apfaudio/tiliqua/gateware/docs/_static/tiliqua-back.jpg

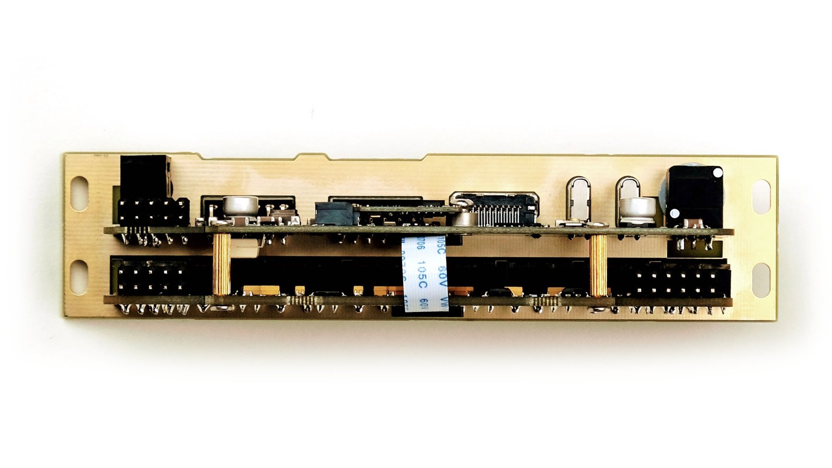
gateware/docs/_static/tiliqua-back.jpg
