apfaudio/tiliqua/gateware/docs/_static/devlog_mar25/plots/mipi_ttl/mipi_100khz.png

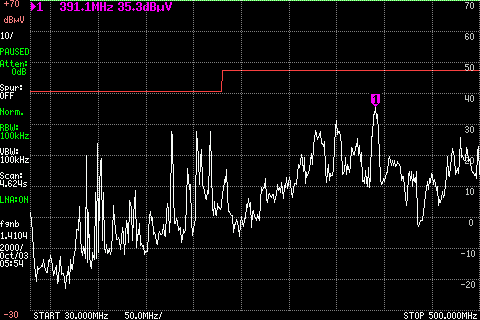
gateware/docs/_static/devlog_mar25/plots/mipi_ttl/mipi_100khz.png
