apfaudio/tiliqua/gateware/docs/_static/devlog_mar25/plots/mipi_ttl/ttl_100khz.png

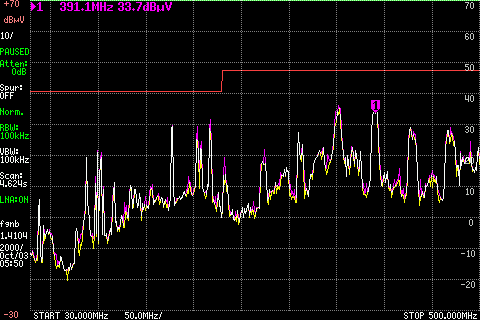
gateware/docs/_static/devlog_mar25/plots/mipi_ttl/ttl_100khz.png
