apfaudio/tiliqua/gateware/docs/_static/devlog_mar25/plots/r4_ea8c_850khz.png

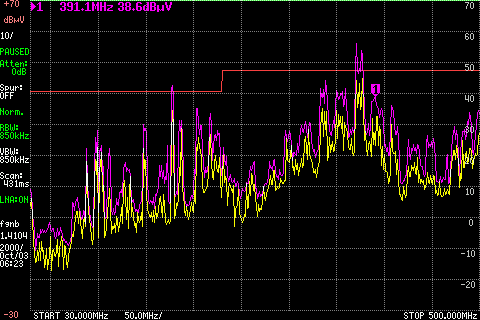
gateware/docs/_static/devlog_mar25/plots/r4_ea8c_850khz.png
