apfaudio/tiliqua/gateware/docs/_static/devlog_mar25/plots/r4_main_macro_osc_0p1ssc_100khz.png

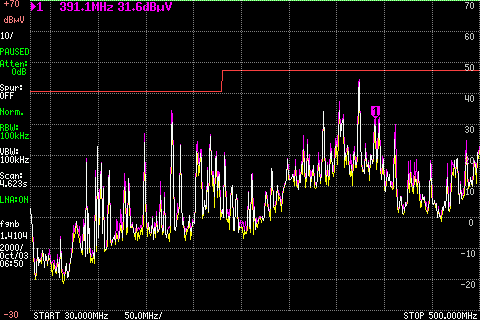
gateware/docs/_static/devlog_mar25/plots/r4_main_macro_osc_0p1ssc_100khz.png
