apfaudio/tiliqua/gateware/src/tiliqua/dsp.py

# Copyright (c) 2024 S. Holzapfel <me@sebholzapfel.com>
#
# SPDX-License-Identifier: CERN-OHL-S-2.0
#

"""Streaming DSP library with a strong focus on audio."""

import math

from amaranth              import *
from amaranth.lib          import wiring, data, stream, enum
from amaranth.lib.wiring   import In, Out
from amaranth.lib.fifo     import SyncFIFOBuffered, AsyncFIFOBuffered
from amaranth.lib.memory   import Memory
from amaranth.utils        import exact_log2, ceil_log2

from scipy import signal

from amaranth_future       import fixed
from tiliqua               import mac

from tiliqua.eurorack_pmod import ASQ # hardware native fixed-point sample type

# dummy values used to hook up to unused stream in/out ports, so they don't block forever
ASQ_READY = stream.Signature(ASQ, always_ready=True).flip().create()
ASQ_VALID = stream.Signature(ASQ, always_valid=True).create()

class Split(wiring.Component):

    """
    Consumes payloads from a single stream and splits it into multiple independent streams.
    This component may be instantiated in 2 modes depending on the value of :py:`replicate`:

    - **Channel splitter** (:py:`replicate == False`):
        The incoming stream has an :py:`data.ArrayLayout` signature. Each payload in the
        :py:`data.ArrayLayout` becomes an independent outgoing stream. :py:`n_channels`
        must match the number of payloads in the :py:`data.ArrayLayout`.

    - **Channel replicater** (:py:`replicate == True`):
        The incoming stream has a single payload. Each payload in the incoming stream
        is replicated and at the output appears as :py:`n_channels` independent streams,
        which produce the same values, however may be synchronized/consumed independently.

    This class is inspired by previous work in the lambdalib and LiteX projects.
    """

    def __init__(self, n_channels, replicate=False, source=None):
        """
        n_channels : int
            The number of independent output streams. See usage above.
        replicate : bool, optional
            See usage above.
        source : stream, optional
            Optional incoming stream to pass through to :py:`wiring.connect` on
            elaboration. This argument means you do not have to hook up :py:`self.i`
            and can make some pipelines a little easier to read.
        """
        self.n_channels = n_channels
        self.replicate  = replicate
        self.source     = source

        if self.replicate:
            super().__init__({
                "i": In(stream.Signature(ASQ)),
                "o": Out(stream.Signature(ASQ)).array(n_channels),
            })
        else:
            super().__init__({
                "i": In(stream.Signature(data.ArrayLayout(ASQ, n_channels))),
                "o": Out(stream.Signature(ASQ)).array(n_channels),
            })

    def elaborate(self, platform):
        m = Module()

        done = Signal(self.n_channels)

        m.d.comb += self.i.ready.eq(Cat([self.o[n].ready | done[n] for n in range(self.n_channels)]).all())
        m.d.comb += [self.o[n].valid.eq(self.i.valid & ~done[n]) for n in range(self.n_channels)]

        if self.replicate:
            m.d.comb += [self.o[n].payload.eq(self.i.payload) for n in range(self.n_channels)]
        else:
            m.d.comb += [self.o[n].payload.eq(self.i.payload[n]) for n in range(self.n_channels)]

        flow = [self.o[n].valid & self.o[n].ready
                for n in range(self.n_channels)]
        end  = Cat([flow[n] | done[n]
                    for n in range(self.n_channels)]).all()
        with m.If(end):
            m.d.sync += done.eq(0)
        with m.Else():
            for n in range(self.n_channels):
                with m.If(flow[n]):
                    m.d.sync += done[n].eq(1)

        if self.source is not None:
            wiring.connect(m, self.source, self.i)

        return m

    def wire_ready(self, m, channels):
        """Set out channels as permanently READY so they don't block progress."""
        for n in channels:
            wiring.connect(m, self.o[n], ASQ_READY)

class Merge(wiring.Component):

    """
    Consumes payloads from multiple independent streams and merges them into a single stream.

    This class is inspired by previous work in the lambdalib and LiteX projects.
    """

    def __init__(self, n_channels, sink=None):
        """
        n_channels : int
            The number of independent incoming streams.
        sink : stream, optional
            Optional outgoing stream to pass through to :py:`wiring.connect` on
            elaboration. This argument means you do not have to hook up :py:`self.o`
            and can make some pipelines a little easier to read.
        """
        self.n_channels = n_channels
        self.sink       = sink
        super().__init__({
            "i": In(stream.Signature(ASQ)).array(n_channels),
            "o": Out(stream.Signature(data.ArrayLayout(ASQ, n_channels))),
        })

    def elaborate(self, platform):
        m = Module()

        m.d.comb += [self.i[n].ready.eq(self.o.ready & self.o.valid) for n in range(self.n_channels)]
        m.d.comb += [self.o.payload[n].eq(self.i[n].payload) for n in range(self.n_channels)]
        m.d.comb += self.o.valid.eq(Cat([self.i[n].valid for n in range(self.n_channels)]).all())

        if self.sink is not None:
            wiring.connect(m, self.o, self.sink)

        return m

    def wire_valid(self, m, channels):
        """Set in channels as permanently VALID so they don't block progress."""
        for n in channels:
            wiring.connect(m, stream.Signature(ASQ, always_valid=True).create(), self.i[n])

def connect_remap(m, stream_o, stream_i, mapping):
    """
    Connect 2 streams, bypassing normal wiring.connect() checks
    that the signatures match. This allows easily remapping fields when
    you are trying to connect streams with different signatures.

    For example, say I have a stream with an ArrayLayout payload and want to
    map it to a different stream with a StructLayout payload, and the underlying
    bit-representation of both layouts do not match, I can remap using:

    .. code-block:: python

        dsp.connect_remap(m, vca_merge2a.o, vca0.i, lambda o, i : [
            i.payload.x   .eq(o.payload[0]),
            i.payload.gain.eq(o.payload[1] << 2)
        ])

    This is a bit of a hack. TODO perhaps implement this as a StreamConverter
    such that we can still use wiring.connect?.
    """

    m.d.comb += mapping(stream_o, stream_i) + [
        stream_i.valid.eq(stream_o.valid),
        stream_o.ready.eq(stream_i.ready)
    ]

def channel_remap(m, stream_o, stream_i, mapping_o_to_i):
    """
    Connect 2 streams of type :py:`data.ArrayLayout`, with different channel
    counts or channel indices. For example, to connect a source with 4 channels
    to a sink with 2 channels, mapping 0 to 0, 1 to 1, leaving 2 and 3 unconnected:

    .. code-block:: python

        s1 = stream.Signature(data.ArrayLayout(ASQ, 4)).create()
        s2 = stream.Signature(data.ArrayLayout(ASQ, 2)).create()
        dsp.channel_remap(m, s1, s2, {0: 0, 1: 1})

    This also works the other way around, to connect e.g. a source with 2 channels to
    a sink with 4 channels. The stream will make progress however the value of the
    payloads in any unmapped output channels is undefined.
    """
    def remap(o, i):
        connections = []
        for k in mapping_o_to_i:
            connections.append(i.payload[mapping_o_to_i[k]].eq(o.payload[k]))
        return connections
    return connect_remap(m, stream_o, stream_i, remap)


class VCA(wiring.Component):

    """
    Voltage Controlled Amplifier (simple multiplier with saturation).
    Output values are clipped to fit in the output type.

    Members
    -------
    i : :py:`In(stream.Signature(data.ArrayLayout(itype, 2)))`
        2-channel input stream.
    o : :py:`Out(stream.Signature(otype))`
        Output stream, :py:`i.payload[0] * i.payload[1]`.
    """

    def __init__(self, itype=mac.SQNative, otype=ASQ, macp=None):
        self.macp = macp or mac.MAC.default()
        super().__init__({
            "i": In(stream.Signature(data.ArrayLayout(itype, 2))),
            "o": Out(stream.Signature(otype))
        })

    def elaborate(self, platform):
        m = Module()

        m.submodules.macp = mp = self.macp

        with m.FSM() as fsm:

            with m.State('WAIT-VALID'):
                m.d.comb += self.i.ready.eq(1),
                with m.If(self.i.valid):
                   m.next = 'MAC'

            with m.State('MAC'):
                with mp.Multiply(m, a=self.i.payload[0], b=self.i.payload[1]):
                    m.d.sync += self.o.payload.eq(mp.z.saturate(self.o.payload.shape()))
                    m.next = 'WAIT-READY'

            with m.State('WAIT-READY'):
                m.d.comb += self.o.valid.eq(1),
                with m.If(self.o.ready):
                    m.next = 'WAIT-VALID'

        return m

class SawNCO(wiring.Component):
    """
    Sawtooth Numerically Controlled Oscillator.

    Often this can be simply routed into a LUT waveshaper for any other waveform type.

    Members
    -------
    i : :py:`In(stream.Signature(data.StructLayout)`
        Input stream, with fields :py:`freq_inc` (linear frequency) and
        :py:`phase` (phase offset). One output sample is produced for each
        input sample.
    o : :py:`Out(stream.Signature(ASQ))`
        Output stream, values sweep from :py:`ASQ.min()` to :py:`ASQ.max()`.
    """
    i: In(stream.Signature(data.StructLayout({
            "freq_inc": ASQ,
            "phase": ASQ,
        })))
    o: Out(stream.Signature(ASQ))

    def __init__(self, extra_bits=16, shift=6):
        self.extra_bits = extra_bits
        self.shift = shift
        super().__init__()

    def elaborate(self, platform):
        m = Module()

        s = Signal(fixed.SQ(self.extra_bits, ASQ.f_bits))

        out_no_phase_mod = Signal(ASQ)

        m.d.comb += [
            self.o.valid.eq(self.i.valid),
            self.i.ready.eq(self.o.ready),
            out_no_phase_mod.eq(s >> self.shift),
            self.o.payload.eq(
                out_no_phase_mod + self.i.payload.phase),
        ]

        with m.If(self.i.valid & self.o.ready):
            m.d.sync += s.eq(s + self.i.payload.freq_inc),

        return m

class Trigger(wiring.Component):

    """
    When trigger condition is met, output is set to 1, for 1 stream cycle.

    Currently this only implements rising edge trigger.
    """

    i: In(stream.Signature(data.StructLayout({
            "sample":    ASQ,
            "threshold": ASQ,
        })))
    o: Out(stream.Signature(unsigned(1)))

    def elaborate(self, platform):
        m = Module()

        trigger = Signal()
        l_sample = Signal(shape=ASQ)

        m.d.comb += [
            self.o.valid.eq(self.i.valid),
            self.i.ready.eq(self.o.ready),
        ]

        with m.If(self.i.valid & self.o.ready):
            m.d.sync += l_sample.eq(self.i.payload.sample)
            m.d.comb += [
                self.o.payload.eq(
                    (l_sample              < self.i.payload.threshold) &
                    (self.i.payload.sample >= self.i.payload.threshold)
                ),
            ]

        return m

class Ramp(wiring.Component):

    """
    If trigger strobes a 1, ramps from -1 to 1, staying at 1 until retriggered.
    A retrigger mid-ramp does not restart the ramp until the output has reached 1.
    """

    i: In(stream.Signature(data.StructLayout({
            "trigger":  unsigned(1),
            "td":       ASQ, # time delta
        })))
    o: Out(stream.Signature(ASQ))

    def __init__(self, extra_bits=16, shift=6):
        self.extra_bits = extra_bits
        self.shift = shift
        super().__init__()

    def elaborate(self, platform):
        m = Module()

        s = Signal(fixed.SQ(self.extra_bits+1, ASQ.f_bits))

        m.d.comb += [
            self.o.valid.eq(self.i.valid),
            self.i.ready.eq(self.o.ready),
            self.o.payload.eq(s >> self.shift),
        ]

        with m.If(self.i.valid & self.o.ready):
            with m.If(self.o.payload > fixed.Const(0.95, shape=ASQ)):
                with m.If(self.i.payload.trigger):
                    m.d.sync += s.eq(ASQ.min() << self.shift)
            with m.Else():
                m.d.sync += s.eq(s + self.i.payload.td)

        return m

class WaveShaper(wiring.Component):

    """
    Waveshaper that maps x to f(x), where the function must be
    stateless so we can precompute a mapping lookup table.

    Linear interpolation is used between lut elements.
    """

    i: In(stream.Signature(ASQ))
    o: Out(stream.Signature(ASQ))

    def __init__(self, lut_function=None, lut_size=512, continuous=False, macp=None):
        self.lut_size = lut_size
        self.lut_addr_width = exact_log2(lut_size)
        self.continuous = continuous
        self.macp = macp or mac.MAC.default()

        # build LUT such that we can index into it using 2s
        # complement and pluck out results with correct sign.
        self.lut = []
        for i in range(lut_size):
            x = None
            if i < lut_size//2:
                x = 2*i / lut_size
            else:
                x = 2*(i - lut_size) / lut_size
            fx = lut_function(x)
            if fx > ASQ.max().as_float() or fx < ASQ.min().as_float():
                print(f"WARN: WaveShaper `lut_function` generates {fx:.5f} which is outside "
                      f"[{ASQ.min().as_float():.5f}..{ASQ.max().as_float():.5f}] (will be clamped)")
            self.lut.append(fixed.Const(fx, shape=ASQ, clamp=True))

        super().__init__()

    def elaborate(self, platform):
        m = Module()

        m.submodules.macp = mp = self.macp

        m.submodules.mem = mem = Memory(
            shape=ASQ, depth=self.lut_size, init=self.lut)
        rport = mem.read_port()

        ltype = fixed.SQ(self.lut_addr_width, ASQ.f_bits-self.lut_addr_width+1)

        x = Signal(ltype)
        y = Signal(ASQ)
        read0 = Signal(ASQ)
        read1 = Signal(ASQ)

        trunc = Signal()

        with m.FSM() as fsm:

            with m.State('WAIT-VALID'):
                m.d.comb += self.i.ready.eq(1),
                with m.If(self.i.valid):
                    m.d.sync += x.eq(self.i.payload << (ltype.i_bits-1))
                    m.d.sync += y.eq(0)
                    m.next = 'ADDR0'

            with m.State('ADDR0'):
                m.d.comb += [
                    rport.en.eq(1),
                ]
                # is this a function where f(+1) ~= f(-1)
                if self.continuous:
                    m.d.comb += rport.addr.eq(x.truncate()+1)
                else:
                    with m.If((x.truncate()).as_value() ==
                              2**(self.lut_addr_width-1)-1):
                        m.d.comb += trunc.eq(1)
                        m.d.comb += rport.addr.eq(x.truncate())
                    with m.Else():
                        m.d.comb += rport.addr.eq(x.truncate()+1)
                m.next = 'READ0'

            with m.State('READ0'):
                m.d.sync += read0.eq(rport.data)
                m.d.comb += [
                    rport.addr.eq(x.truncate()),
                    rport.en.eq(1),
                ]
                m.next = 'READ1'

            with m.State('READ1'):
                m.d.sync += read1.eq(rport.data)
                m.next = 'MAC0'

            with m.State('MAC0'):
                with mp.Multiply(m, a=read0, b=x-x.truncate()):
                    m.d.sync += y.eq(mp.z)
                    m.next = 'MAC1'

            with m.State('MAC1'):
                with mp.Multiply(m, a=read1, b=(x.truncate()-x+1)):
                    m.d.sync += self.o.payload.eq(y + mp.z)
                    m.next = 'WAIT-READY'

            with m.State('WAIT-READY'):
                m.d.comb += [
                    self.o.valid.eq(1),
                ]
                with m.If(self.o.ready):
                    m.next = 'WAIT-VALID'


        return m

class SVF(wiring.Component):

    """
    Oversampled Chamberlin State Variable Filter.

    Filter `cutoff` and `resonance` are tunable at the system sample rate.

    Highpass, lowpass, bandpass routed out on stream payloads `hp`, `lp`, `bp`.

    Reference: Fig.3 in https://arxiv.org/pdf/2111.05592
    """

    def __init__(self, sq=ASQ, macp=None):
        self.sq = sq
        self.macp = macp or mac.MAC.default()
        super().__init__({
            "i": In(stream.Signature(data.StructLayout({
                    "x": sq,
                    "cutoff": sq,
                    "resonance": sq,
                }))),
            "o": Out(stream.Signature(data.StructLayout({
                    "hp": sq,
                    "lp": sq,
                    "bp": sq,
                }))),
        })

    def elaborate(self, platform):
        m = Module()

        m.submodules.macp = mp = self.macp

        x     = Signal(mac.SQNative)
        kK    = Signal.like(x)
        kQinv = Signal.like(x)

        abp   = Signal(fixed.SQ(mac.SQNative.i_bits, mac.SQNative.f_bits+2))
        alp   = Signal.like(abp)
        ahp   = Signal.like(alp)

        # internal oversampling iterations
        n_oversample = 2
        oversample = Signal(range(n_oversample))

        with m.FSM() as fsm:

            with m.State('WAIT-VALID'):
                m.d.comb += self.i.ready.eq(1),
                with m.If(self.i.valid):
                   m.d.sync += x.eq(self.i.payload.x),
                   m.d.sync += oversample.eq(0)
                   with m.If(self.i.payload.cutoff >= 0):
                       m.d.sync += kK.eq(self.i.payload.cutoff)
                   with m.If(self.i.payload.resonance >= 0):
                       m.d.sync += kQinv.eq(self.i.payload.resonance)
                   m.next = 'MAC0'

            with m.State('MAC0'):
                # alp = abp*kK + alp
                with mp.Multiply(m, a=abp, b=kK):
                    m.d.sync += alp.eq(mp.z + alp)
                    m.next = 'MAC1'

            with m.State('MAC1'):
                # ahp = abp*-kQinv + (x - alp)
                with mp.Multiply(m, a=abp, b=-kQinv):
                    m.d.sync += ahp.eq(mp.z + (x - alp))
                    m.next = 'MAC2'

            with m.State('MAC2'):
                # abp = ahp*kK + abp
                with mp.Multiply(m, a=ahp, b=kK):
                    m.d.sync += abp.eq(mp.z + abp)
                    m.next = 'OVER'

            with m.State('OVER'):
                with m.If(oversample == n_oversample - 1):
                    m.next = 'WAIT-READY'
                with m.Else():
                    m.d.sync += oversample.eq(oversample + 1)
                    m.next = 'MAC0'

            with m.State('WAIT-READY'):
                m.d.comb += [
                    self.o.valid.eq(1),
                    self.o.payload.hp.eq(ahp >> 1),
                    self.o.payload.lp.eq(alp >> 1),
                    self.o.payload.bp.eq(abp >> 1),
                ]
                with m.If(self.o.ready):
                    m.next = 'WAIT-VALID'

        return m

class DCBlock(wiring.Component):

    """
    Loosely based on:
    https://dspguru.com/dsp/tricks/fixed-point-dc-blocking-filter-with-noise-shaping/
    """

    def __init__(self, pole=0.999, sq=ASQ, macp=None):
        self.macp = macp or mac.MAC.default()
        self.pole = pole
        self.sq = sq
        super().__init__({
            "i": In(stream.Signature(sq)),
            "o": Out(stream.Signature(sq)),
        })

    def elaborate(self, platform):

        m = Module()

        m.submodules.macp = mp = self.macp

        kA    = fixed.Const((1-self.pole), self.sq)

        x     = Signal(self.sq)
        y     = Signal(self.sq)

        acc   = Signal(mac.SQRNative)

        m.d.comb += self.o.payload.eq(acc)

        with m.FSM() as fsm:

            with m.State('WAIT-VALID'):
                m.d.comb += self.i.ready.eq(1)
                with m.If(self.i.valid):
                   m.d.sync += [
                       x.eq(self.i.payload),
                       acc.eq(acc - x),
                   ]
                   m.next = 'MAC0'

            with m.State('MAC0'):
                with mp.Multiply(m, a=y, b=kA):
                    m.d.sync += acc.eq((acc - mp.z) + x)
                    m.next = 'WAIT-READY'

            with m.State('WAIT-READY'):
                m.d.comb += self.o.valid.eq(1)
                with m.If(self.o.ready):
                    m.d.sync += y.eq(acc)
                    m.next = 'WAIT-VALID'

        return m



class KickFeedback(Elaboratable):
    """
    Inject a single dummy (garbage) sample after reset between
    two streams. This is necessary to break infinite blocking
    after reset if streams are set up in a feedback loop.
    """
    def __init__(self, o, i):
        self.o = o
        self.i = i
    def elaborate(self, platform):
        m = Module()
        wiring.connect(m, self.o, self.i)
        with m.FSM() as fsm:
            with m.State('KICK'):
                m.d.comb += self.i.valid.eq(1)
                with m.If(self.i.ready):
                    m.next = 'FORWARD'
            with m.State('FORWARD'):
                pass
        return m

def connect_feedback_kick(m, o, i):
    m.submodules += KickFeedback(o, i)

class PitchShift(wiring.Component):

    """
    Granular pitch shifter. Works by crossfading 2 separately
    tracked taps on a delay line. As a result, maximum grain
    size is the delay line 'max_delay' // 2.

    The delay line tap itself must be hooked up to the input
    source from outside this component (this allows multiple
    shifters to share a single delay line).
    """

    def __init__(self, tap, xfade=256, macp=None):
        assert xfade <= (tap.max_delay // 4)
        self.tap        = tap
        self.xfade      = xfade
        self.xfade_bits = exact_log2(xfade)
        # delay type: integer component is index into delay line
        # +1 is necessary so that we don't overflow on adding grain_sz.
        self.dtype = fixed.SQ(self.tap.addr_width+2, 8)
        self.macp = macp or mac.MAC.default()
        super().__init__({
            "i": In(stream.Signature(data.StructLayout({
                    "pitch": self.dtype,
                    "grain_sz": unsigned(exact_log2(tap.max_delay)),
                  }))),
            "o": Out(stream.Signature(ASQ)),
        })

    def elaborate(self, platform):
        m = Module()

        m.submodules.macp = mp = self.macp

        # Current position in delay line 0, 1 (+= pitch every sample)
        delay0 = Signal(self.dtype)
        delay1 = Signal(self.dtype)
        # Last samples from delay lines
        sample0 = Signal(ASQ)
        sample1 = Signal(ASQ)
        # Envelope values
        env0 = Signal(ASQ)
        env1 = Signal(ASQ)
        output = Signal(ASQ)

        s    = Signal(self.dtype)
        m.d.comb += s.eq(delay0 + self.i.payload.pitch)

        # Last latched grain size, pitch
        grain_sz_latched = Signal(self.i.payload.grain_sz.shape())

        # Second tap always uses second half of delay line.
        m.d.comb += delay1.eq(delay0 + grain_sz_latched)

        with m.FSM() as fsm:
            with m.State('WAIT-VALID'):
                m.d.comb += self.i.ready.eq(1),
                with m.If(self.i.valid):
                    pitch    = self.i.payload.pitch
                    grain_sz = self.i.payload.grain_sz
                    m.d.sync += grain_sz_latched.eq(grain_sz)
                    with m.If((delay0 + pitch) < fixed.Const(0, shape=self.dtype)):
                        m.d.sync += delay0.eq(delay0 + grain_sz + pitch)
                    with m.Elif((delay0 + pitch) > fixed.Value.cast(grain_sz)):
                        m.d.sync += delay0.eq(delay0 + pitch - grain_sz)
                    with m.Else():
                        m.d.sync += delay0.eq(delay0 + pitch)
                    m.next = 'TAP0'
            with m.State('TAP0'):
                m.d.comb += [
                    self.tap.o.ready.eq(1),
                    self.tap.i.valid.eq(1),
                    self.tap.i.payload.eq(1+delay0.truncate() >> delay0.f_bits),
                ]
                with m.If(self.tap.o.valid):
                    m.d.comb += self.tap.i.valid.eq(0),
                    m.d.sync += sample0.eq(self.tap.o.payload)
                    m.next = 'TAP1'
            with m.State('TAP1'):
                m.d.comb += [
                    self.tap.o.ready.eq(1),
                    self.tap.i.valid.eq(1),
                    self.tap.i.payload.eq(delay1.truncate() >> delay1.f_bits),
                ]
                with m.If(self.tap.o.valid):
                    m.d.comb += self.tap.i.valid.eq(0),
                    m.d.sync += sample1.eq(self.tap.o.payload)
                    m.next = 'ENV'
            with m.State('ENV'):
                with m.If(delay0 < self.xfade):
                    # Map delay0 <= [0, xfade] to env0 <= [0, 1]
                    m.d.sync += [
                        env0.eq(delay0 >> self.xfade_bits),
                        env1.eq(ASQ.max() -
                                (delay0 >> self.xfade_bits)),
                    ]
                with m.Else():
                    # If we're outside the xfade, just take tap 0
                    m.d.sync += [
                        env0.eq(ASQ.max()),
                        env1.eq(0),
                    ]
                m.next = 'MAC0'
            with m.State('MAC0'):
                with mp.Multiply(m, a=sample0, b=env0):
                    m.d.sync += self.o.payload.eq(mp.z)
                    m.next = 'MAC1'
            with m.State('MAC1'):
                with mp.Multiply(m, a=sample1, b=env1):
                    m.d.sync += self.o.payload.eq(self.o.payload + mp.z)
                    m.next = 'WAIT-READY'
            with m.State('WAIT-READY'):
                m.d.comb += self.o.valid.eq(1),
                with m.If(self.o.ready):
                    m.d.sync += output.eq(self.o.payload)
                    m.next = 'WAIT-VALID'
        return m

class MatrixMix(wiring.Component):

    """
    Matrix mixer with tunable coefficients and configurable
    input & output channel count. Uses a single multiplier.

    Coefficients must fit inside the self.ctype declared below.
    Coefficients can be updated in real-time by writing them
    to the `c` stream (position `o_x`, `i_y`, value `v`).
    """

    def __init__(self, i_channels, o_channels, coefficients):

        assert(len(coefficients)       == i_channels)
        assert(len(coefficients[0])    == o_channels)

        self.i_channels = i_channels
        self.o_channels = o_channels

        self.ctype = mac.SQNative

        coefficients_flat = [
            fixed.Const(x, shape=self.ctype)
            for xs in coefficients
            for x in xs
        ]

        assert(len(coefficients_flat) == i_channels*o_channels)

        # matrix coefficient memory
        self.mem = Memory(
            shape=self.ctype,
            depth=i_channels*o_channels, init=coefficients_flat)

        super().__init__({
            "i": In(stream.Signature(data.ArrayLayout(ASQ, i_channels))),
            "c": In(stream.Signature(data.StructLayout({
                "o_x": unsigned(exact_log2(self.o_channels)),
                "i_y": unsigned(exact_log2(self.i_channels)),
                "v":   self.ctype
                }))),
            "o": Out(stream.Signature(data.ArrayLayout(ASQ, o_channels))),
        })

    def elaborate(self, platform):
        m = Module()

        m.submodules.mem = self.mem
        wport = self.mem.write_port()
        rport = self.mem.read_port(transparent_for=(wport,))

        i_latch = Signal(data.ArrayLayout(self.ctype, self.i_channels))
        o_accum = Signal(data.ArrayLayout(
            mac.SQRNative, self.o_channels))

        i_ch   = Signal(exact_log2(self.i_channels))
        o_ch   = Signal(exact_log2(self.o_channels))
        # i/o channel index, one cycle behind.
        l_i_ch = Signal(exact_log2(self.i_channels))
        o_ch_l = Signal(exact_log2(self.o_channels))
        # we've finished all accumulation steps.
        done = Signal(1)

        m.d.comb += [
            rport.en.eq(1),
            rport.addr.eq(Cat(o_ch, i_ch)),
        ]

        read0 = Signal(self.ctype)

        # coefficient update logic

        with m.If(self.c.ready):
            m.d.comb += [
                wport.addr.eq(Cat(self.c.payload.o_x, self.c.payload.i_y)),
                wport.en.eq(self.c.valid),
                wport.data.eq(self.c.payload.v),
            ]

        # main multiplications state machine

        with m.FSM() as fsm:
            with m.State('WAIT-VALID'):
                m.d.comb += self.c.ready.eq(1), # permit coefficient updates
                m.d.comb += self.i.ready.eq(1),
                with m.If(self.i.valid):
                    m.d.sync += [
                        o_accum.eq(0),
                        i_ch.eq(0),
                        o_ch.eq(0),
                        done.eq(0),
                    ]
                    # FIXME: assigning each element of the payload is necessary
                    # because assignment of a data.ArrayLayout ignores the
                    # underlying fixed-point types. This should be cleaner!
                    m.d.sync += [
                        i_latch[n].eq(self.i.payload[n])
                        for n in range(self.i_channels)
                    ]
                    m.next = 'NEXT'
            with m.State('NEXT'):
                m.next = 'MAC'
                m.d.sync += [
                    o_ch_l.eq(o_ch),
                    l_i_ch.eq(i_ch),
                ]
                with m.If(o_ch == (self.o_channels - 1)):
                    m.d.sync += o_ch.eq(0)
                    with m.If(i_ch == (self.i_channels - 1)):
                        m.d.sync += done.eq(1)
                    with m.Else():
                        m.d.sync += i_ch.eq(i_ch+1)
                with m.Else():
                    m.d.sync += o_ch.eq(o_ch+1)
            with m.State('MAC'):
                m.next = 'NEXT'
                m.d.sync += [
                    o_accum[o_ch_l].eq(o_accum[o_ch_l] +
                                       (rport.data *
                                        i_latch[l_i_ch]))
                ]
                with m.If(done):
                    m.next = 'LATCH'
            with m.State('LATCH'):
                m.d.sync += [
                    self.o.payload[n].eq(o_accum[n])
                    for n in range(self.o_channels)
                ]
                m.next = 'WAIT-READY'
            with m.State('WAIT-READY'):
                m.d.comb += self.c.ready.eq(1), # permit coefficient updates
                m.d.comb += [
                    self.o.valid.eq(1),
                ]
                with m.If(self.o.ready):
                    m.next = 'WAIT-VALID'

        return m

class FIR(wiring.Component):

    """
    Fixed-point FIR filter that uses a single multiplier.

    This filter contains some optional optimizations to act as an efficient
    interpolator/decimator. For details, see :py:`stride_i`, :py:`stride_o` below.

    Members
    -------
    i : :py:`In(stream.Signature(ASQ))`
        Input stream for sending samples to the filter.
    o : :py:`In(stream.Signature(ASQ))`
        Output stream for getting samples from the filter. There is 1 output
        sample per input sample, presented :py:`filter_order+1` cycles after
        the input sample. For :py:`stride_o > 1`, there is only 1 output
        sample per :py:`stride_o` input samples.
    """

    i: In(stream.Signature(ASQ))
    o: Out(stream.Signature(ASQ))

    def __init__(self,
                 fs:               int,
                 filter_cutoff_hz: int,
                 filter_order:     int,
                 filter_type:      str='lowpass',
                 prescale:         float=1,
                 stride_i:         int=1,
                 stride_o:         int=1):
        """
        fs : int
            Sample rate of the filter, used for calculating FIR coefficients.
        filter_cutoff_hz : int
            Cutoff frequency of the filter, used for calculating FIR coefficients.
        filter_order : int
            Size of the filter (number of coefficients).
        filter_type : str
            Type of the filter passed to :py:`signal.firwin` - :py:`"lowpass"`,
            :py:`"highpass"` or so on.
        prescale : float
            All taps are scaled by :py:`prescale`. This is used in cases where
            you are upsampling and need to preserve energy. Be careful with this,
            it can overflow the tap coefficients (you'll get a warning).
        stride_i : int
            When an FIR filter is used as an interpolator, a common pattern is
            to provide 1 'actual' sample and pad S-1 zeroes for every S
            output samples needed. For any :py:`stride > 1`, the :py:`stride`
            must evenly divide :py:`filter_order` (i.e. no remainder). For
            :py:`stride > 1`, this core applies some optimizations, assuming
            every S'th sample is nonzero, and the rest are zero. This results in
            a factor S reduction in MAC ops (latency) and a factor S reduction in
            RAM needed for sample storage. The tap storage remains of size
            :py:`filter_order` as all taps are still mathematically required.
            The nonzero sample must be the first sample to arrive.
        stride_o : int
            When an FIR filter is used as a decimator, it is common to keep only
            1 sample and discard M-1 samples (if decimating by factor M). For
            :py:`stride_o == M`, only 1 output sample is produced per M input
            samples. This does not reduce LUT/RAM usage, but avoids performing
            MACs to produce samples that will be discarded.
        """
        taps = signal.firwin(numtaps=filter_order, cutoff=filter_cutoff_hz,
                             fs=fs, pass_zero=filter_type, window='hamming')
        assert len(taps) % stride_i == 0
        self.taps_float = taps
        self.prescale   = prescale
        self.stride_i   = stride_i
        self.stride_o   = stride_o
        super().__init__()

    def elaborate(self, platform):
        m = Module()

        # Tap and accumulator sizes

        self.ctype = fixed.SQ(2, ASQ.f_bits)

        n = len(self.taps_float)

        # Filter tap memory and read port

        # If t*prescale overflows, fixed.Const should provide a warning.
        m.submodules.taps_mem = taps_mem = Memory(
            shape=self.ctype, depth=n, init=[
                fixed.Const(t*self.prescale, shape=self.ctype)
                for t in self.taps_float
            ]
        )

        taps_rport = taps_mem.read_port()

        # Input sample memory, write and read port

        m.submodules.x_mem = x_mem = Memory(
            shape=self.ctype, depth=n//self.stride_i, init=[]
        )

        x_wport = x_mem.write_port()
        x_rport = x_mem.read_port(transparent_for=(x_wport,))

        # FIR filter logic

        # Number of MACs performed per sample, up to n/self.stride
        macs   = Signal(range(n))

        # Write position in input sample memory
        w_pos  = Signal(range(n), init=1)

        # Stride position from 0 .. self.stride_i, moves by 1 every
        # input sample to shift taps looked at (even if the input
        # is padded with zeroes)
        stride_i_pos  = Signal(range(self.stride_i), init=0)

        # Stride position from 0 .. self.stride_o, moves by 1 every
        # output sample. For 'stride_o' == M, output sample is only
        # calculated/emitted once per every M samples.
        stride_o_pos  = Signal(range(self.stride_o), init=0)

        # Read indices into tap and sample memories
        ix_tap = Signal(range(n))
        ix_rd  = Signal(range(n))

        # MAC variables: y = a * b
        a  = Signal(self.ctype)
        b  = Signal(self.ctype)
        y  = Signal(self.ctype)

        m.d.comb += taps_rport.en.eq(1)
        m.d.comb += taps_rport.addr.eq(ix_tap)
        m.d.comb += x_wport.data.eq(self.i.payload)
        m.d.comb += x_rport.addr.eq(ix_rd)
        m.d.comb += x_rport.en.eq(1)

        with m.If(w_pos == (n//self.stride_i - 1)):
            m.d.comb += x_wport.addr.eq(0)
        with m.Else():
            m.d.comb += x_wport.addr.eq(w_pos+1)

        valid = Signal()

        with m.FSM() as fsm:
            with m.State('WAIT-VALID'):
                m.d.comb += self.i.ready.eq(1),
                with m.If(self.i.valid):
                    with m.If(stride_i_pos == 0):
                        m.d.comb += x_wport.en.eq(1)
                    # Set up first MAC combinatorially
                    m.d.comb += x_rport.addr.eq(x_wport.addr)
                    m.d.comb += taps_rport.addr.eq(stride_i_pos)
                    # Subsequent MACs use ix_rd / ix_tap.
                    m.d.sync += [
                        ix_rd.eq(w_pos),
                        ix_tap.eq(stride_i_pos + self.stride_i),
                        y.eq(0),
                        macs.eq(0),
                    ]

                    with m.If(stride_o_pos == 0):
                        m.next = "MAC"
                    with m.Else():
                        m.next = "WAIT-READY"

            with m.State("MAC"):
                m.d.comb += [
                    a.eq(x_rport.data),
                    b.eq(taps_rport.data),
                ]
                m.d.sync += [
                    y.eq(y + (a * b)),
                    macs.eq(macs+1),
                ]
                # next tap read position
                m.d.sync += ix_tap.eq(ix_tap + self.stride_i),
                # next sample read position
                with m.If(ix_rd == 0):
                    m.d.sync += ix_rd.eq((n//self.stride_i - 1))
                with m.Else():
                    m.d.sync += ix_rd.eq(ix_rd - 1),
                # done?
                with m.If(macs == (n//self.stride_i - 1)):
                    m.next = "WAIT-READY"

            with m.State('WAIT-READY'):

                # if stride_o indicates this sample should be discarded, never
                # assert 'valid', simply update the stride counters and jump
                # straight back to 'WAIT-VALID'.

                m.d.comb += [
                    self.o.valid.eq(stride_o_pos == 0),
                    self.o.payload.eq(y)
                ]

                with m.If(self.o.ready | (stride_o_pos != 0)):

                    # update write and stride_i offsets.
                    with m.If(stride_i_pos == (self.stride_i - 1)):
                        m.d.sync += stride_i_pos.eq(0)
                        with m.If(w_pos == (n//self.stride_i - 1)):
                            m.d.sync += w_pos.eq(0)
                        with m.Else():
                            m.d.sync += w_pos.eq(w_pos+1)
                    with m.Else():
                        m.d.sync += stride_i_pos.eq(stride_i_pos+1)

                    # update stride_o index
                    with m.If(stride_o_pos == (self.stride_o - 1)):
                        m.d.sync += stride_o_pos.eq(0)
                    with m.Else():
                        m.d.sync += stride_o_pos.eq(stride_o_pos + 1)

                    m.next = 'WAIT-VALID'

        return m

class Resample(wiring.Component):

    """
    Polyphase fractional resampler.

    Upsamples by factor N, filters the result, then downsamples by factor M.
    The upsampling action zero-pads before applying the low-pass filter, so
    the low-pass filter coefficients are prescaled by N to preserve total energy.

    The underlying FIR interpolator only performs MACs on non-padded input samples,
    (and for output samples which are not discarded), which can make a big difference
    for large upsampling/interpolating ratios, and is what makes this a polyphase
    resampler - time complexity per output sample proportional to O(fir_order/N).

    Members
    -------
    i : :py:`In(stream.Signature(ASQ))`
        Input stream for sending samples to the resampler at sample rate :py:`fs_in`.
    o : :py:`In(stream.Signature(ASQ))`
        Output stream for getting samples from the resampler. Samples are produced
        at a rate determined by :py:`fs_in * (n_up / m_down)`.
    """

    i: In(stream.Signature(ASQ))
    o: Out(stream.Signature(ASQ))

    def __init__(self,
                 fs_in:      int,
                 n_up:       int,
                 m_down:     int,
                 bw:         float=0.4,
                 order_mult: int=5):
        """
        fs_in : int
            Expected sample rate of incoming samples, used for calculating filter coefficients.
        n_up : int
            Numerator of the resampling ratio. Samples are produced at :py:`fs_in * (n_up / m_down)`.
            If :py:`n_up` and :py:`m_down` share a common factor, the internal resampling ratio is reduced.
        m_down : int
            Denominator of the resampling ratio. Samples are produced at :py:`fs_in * (n_up / m_down)`.
            If :py:`n_up` and :py:`m_down` share a common factor, the internal resampling ratio is reduced.
        bw : float
            Bandwidth (0 to 1, proportion of the nyquist frequency) of the resampling filter.
        order_mult : int
            Filter order multiplier, determines number of taps in underlying FIR filter. The
            underlying tap count is determined as :py:`order_factor*max(self.n_up, self.m_down)`,
            rounded up to the next multiple of :py:`n_up` (required for even zero padding).
        """

        gcd = math.gcd(n_up, m_down)
        if gcd > 1:
            print(f"WARN: Resample {n_up}/{m_down} has GCD {gcd}. Using {n_up//gcd}/{m_down//gcd}.")
            n_up = n_up//gcd
            m_down = m_down//gcd

        self.fs_in  = fs_in
        self.n_up   = n_up
        self.m_down = m_down
        self.bw     = bw

        filter_order = order_mult*max(self.n_up, self.m_down)
        if filter_order % self.n_up != 0:
            # If the filter is not divisible by n_up, choose the next largest filter
            # order that is, so that we can use FIR 'stride' (polyphase resampling
            # optimization based on known zero padding).
            filter_order = self.n_up * ((filter_order // self.n_up) + 1)

        self.filt = FIR(
            fs=self.fs_in*self.n_up,
            filter_cutoff_hz=min(self.fs_in*self.bw,
                                 int((self.fs_in*self.bw)*(self.n_up/self.m_down))),
            filter_order=filter_order,
            prescale=self.n_up,
            stride_i=self.n_up,
            stride_o=self.m_down
        )

        super().__init__()

    def elaborate(self, platform):

        m = Module()

        m.submodules.filt = filt = self.filt

        upsampled_signal  = Signal(ASQ)
        upsample_counter  = Signal(range(self.n_up))

        m.d.comb += [
            self.i.ready.eq((upsample_counter == 0) & filt.i.ready),
        ]

        with m.If(filt.i.ready):
            with m.If(self.i.valid & self.i.ready):
                m.d.comb += [
                    filt.i.payload.eq(self.i.payload),
                    filt.i.valid.eq(1),
                ]
                m.d.sync += upsample_counter.eq(self.n_up - 1)
            with m.Elif(upsample_counter > 0):
                m.d.comb += [
                    filt.i.payload.eq(0),
                    filt.i.valid.eq(1),
                ]
                m.d.sync += upsample_counter.eq(upsample_counter - 1)


        wiring.connect(m, filt.o, wiring.flipped(self.o))

        return m

class CountingFollower(wiring.Component):
    """
    Simple unsigned counting follower.

    Output follows the input, getting closer to it by 1 count per :py:`valid` strobe.

    This is quite a cheap way to avoid pops on envelopes.
    """

    def __init__(self, bits=8):
        super().__init__({
            "i": In(stream.Signature(unsigned(bits))),
            "o": Out(stream.Signature(unsigned(bits))),
        })

    def elaborate(self, platform):
        m = Module()
        m.d.comb += self.i.ready.eq(self.o.ready)
        m.d.comb += self.o.valid.eq(self.i.valid)
        with m.If(self.i.valid & self.o.ready):
            with m.If(self.o.payload < self.i.payload):
                m.d.sync += self.o.payload.eq(self.o.payload + 1)
            with m.Elif(self.o.payload > self.i.payload):
                m.d.sync += self.o.payload.eq(self.o.payload - 1)
        return m

def named_submodules(m_submodules, elaboratables, override_name=None):
    """
    Normally, using constructs like:

    .. code-block:: python

        m.submodules += delaylines

    You get generated code with names like U$14 ... as Amaranth's
    namer doesn't give such modules a readable name.

    Instead, you can do:

    .. code-block:: python

        named_submodules(m.submodules, delaylines)

    And this helper will give each instance a name.

    TODO: is there an idiomatic way of doing this?
    """
    if override_name is None:
        [setattr(m_submodules, f"{type(e).__name__.lower()}{i}", e) for i, e in enumerate(elaboratables)]
    else:
        [setattr(m_submodules, f"{override_name}{i}", e) for i, e in enumerate(elaboratables)]


def connect_peek(m, stream_peek, stream_dst, always_ready=False):
    """
    Nonblocking 'peek', used to tap off an EXISTING stream connection, without
    influencing it, for inspection / plotting purposes.
    """
    m.d.comb += [
        stream_dst.valid.eq(stream_peek.valid & stream_peek.ready),
        stream_dst.payload.eq(stream_peek.payload),
        stream_peek.ready.eq(1) if always_ready else []
    ]

class Duplicate(wiring.Component):
    """
    Simple 'upsampler' that duplicates each input sample N times.

    No filtering is performed - each input sample is simply repeated N times
    in the output stream.

    Members
    -------
    i : :py:`In(stream.Signature(ASQ))`
        Input stream for samples to be upsampled.
    o : :py:`Out(stream.Signature(ASQ))`
        Output stream producing each input sample N times.
    """

    i: In(stream.Signature(ASQ))
    o: Out(stream.Signature(ASQ))

    def __init__(self, n: int):
        self.n = n
        super().__init__()

    def elaborate(self, platform):
        m = Module()
        if self.n == 1:
            wiring.connect(m, wiring.flipped(self.i), self.o)
        else:
            dup_counter = Signal(range(self.n))
            current_sample = Signal(ASQ)
            sample_valid = Signal()
            m.d.comb += self.i.ready.eq(dup_counter == 0)
            with m.If(self.i.valid & self.i.ready):
                m.d.sync += [
                    current_sample.eq(self.i.payload),
                    sample_valid.eq(1),
                    dup_counter.eq(self.n - 1),
                ]
            with m.If(self.o.ready & sample_valid):
                with m.If(dup_counter > 0):
                    m.d.sync += dup_counter.eq(dup_counter - 1)
                with m.Else():
                    m.d.sync += sample_valid.eq(0)
            m.d.comb += [
                self.o.valid.eq(sample_valid),
                self.o.payload.eq(current_sample),
            ]
        return m
